danzolo211/Spotify_Frame/tools/_stand_preview.png

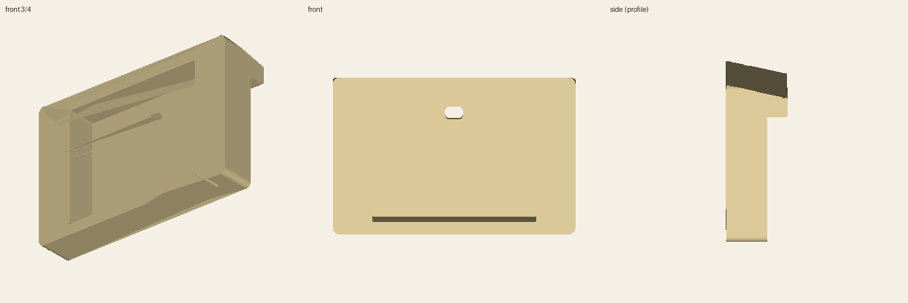
tools/_stand_preview.png
