danzolo211/Spotify_Frame/tools/_v3_cutaway.png

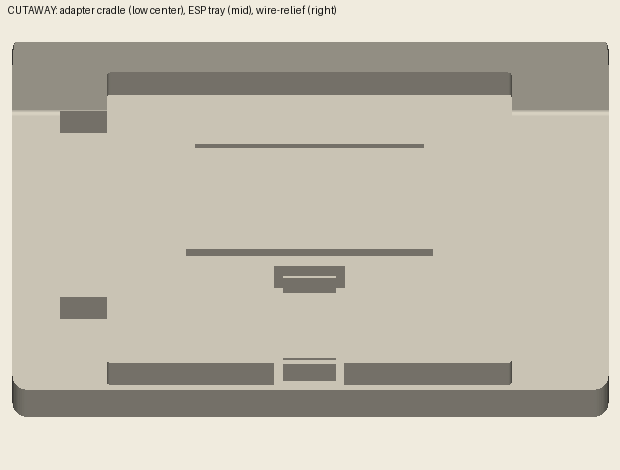
tools/_v3_cutaway.png
