danzolo211/Spotify_Frame/tools/_v3_fit_side.png

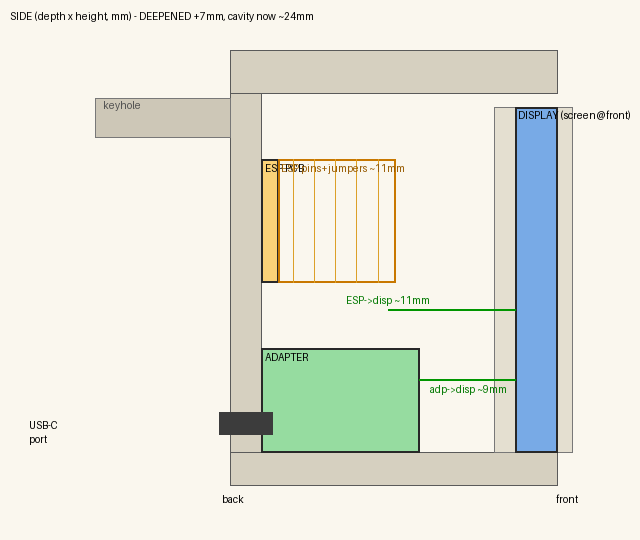
tools/_v3_fit_side.png
