danzolo211/Spotify_Frame/tools/_v3_preview.png

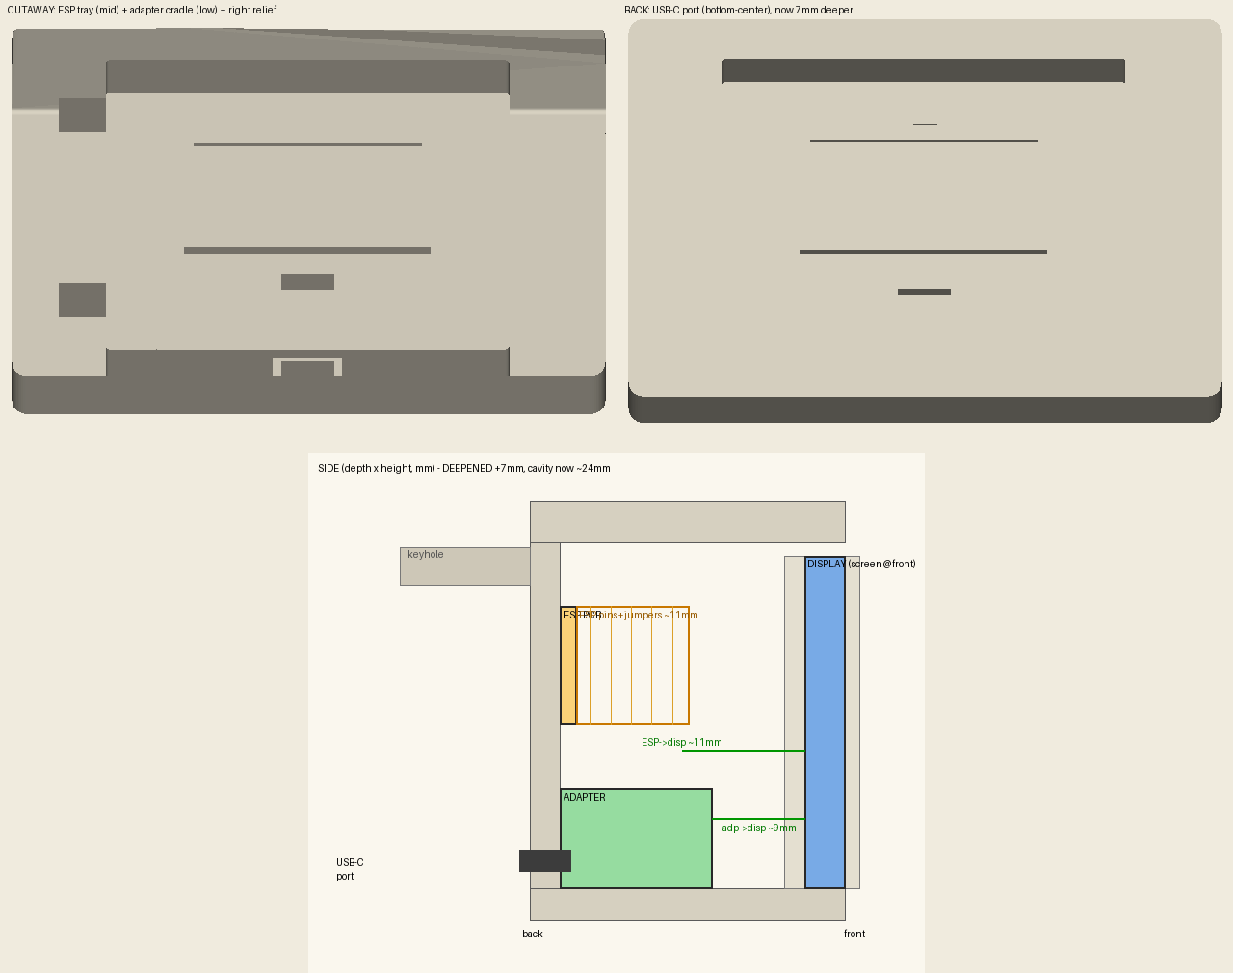
tools/_v3_preview.png
