danzolo211/Spotify_Frame/tools/previews/000_note-flourish.png

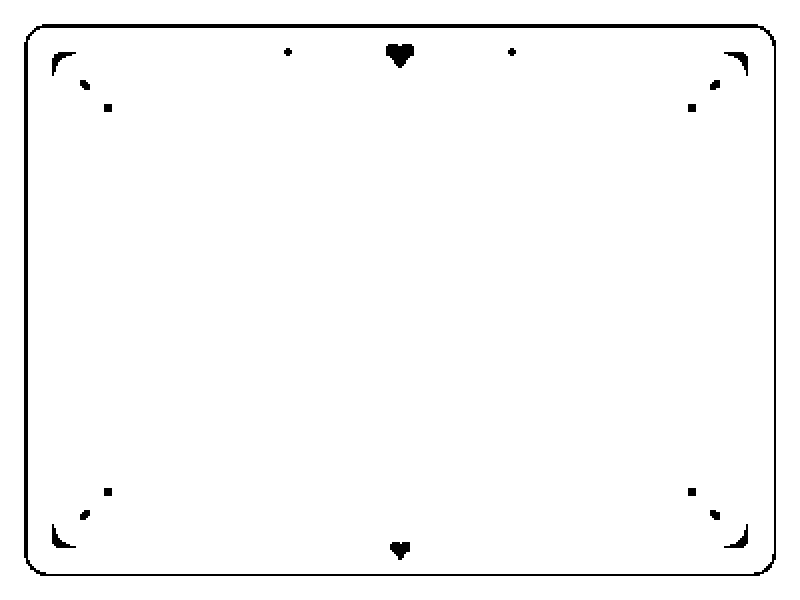
tools/previews/000_note-flourish.png
