danzolo211/Spotify_Frame/tools/previews/001_celebration.png

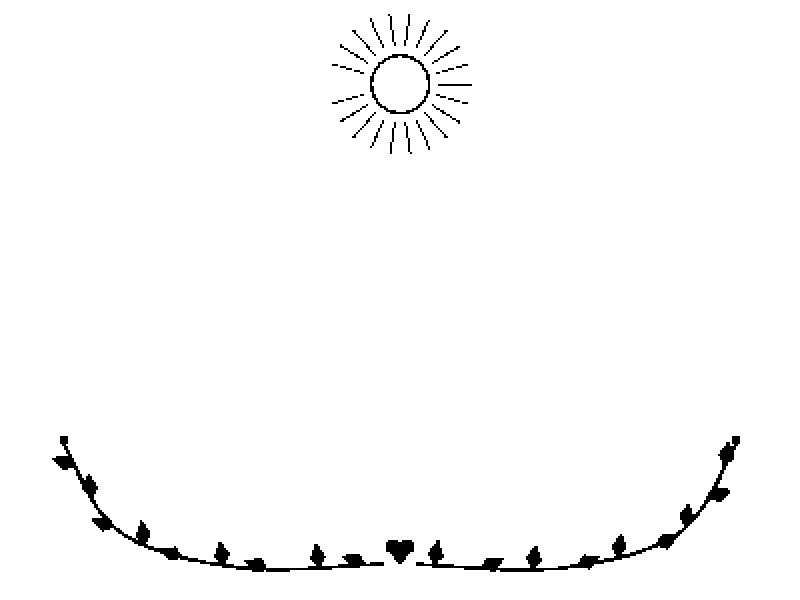
tools/previews/001_celebration.png
