danzolo211/Spotify_Frame/tools/previews/002_golgotha-dawn.png

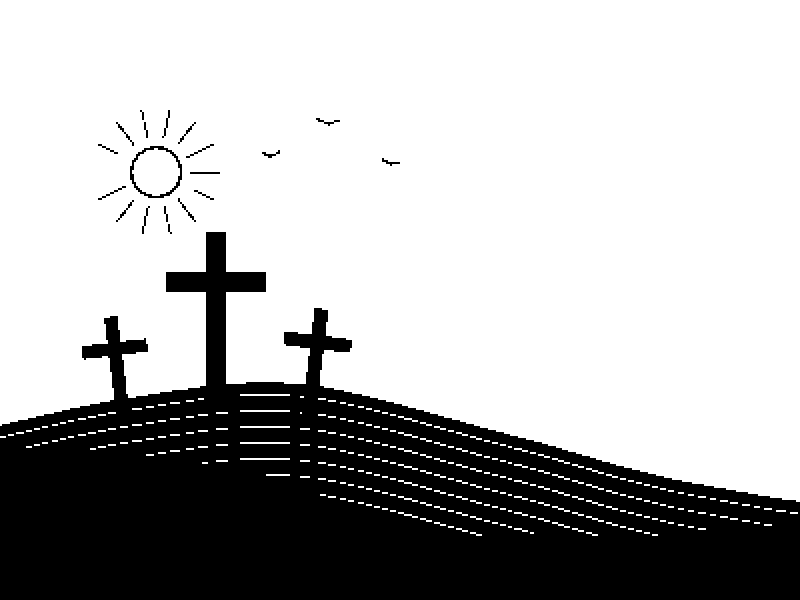
tools/previews/002_golgotha-dawn.png
