danzolo211/Spotify_Frame/tools/previews/003_shepherd.png

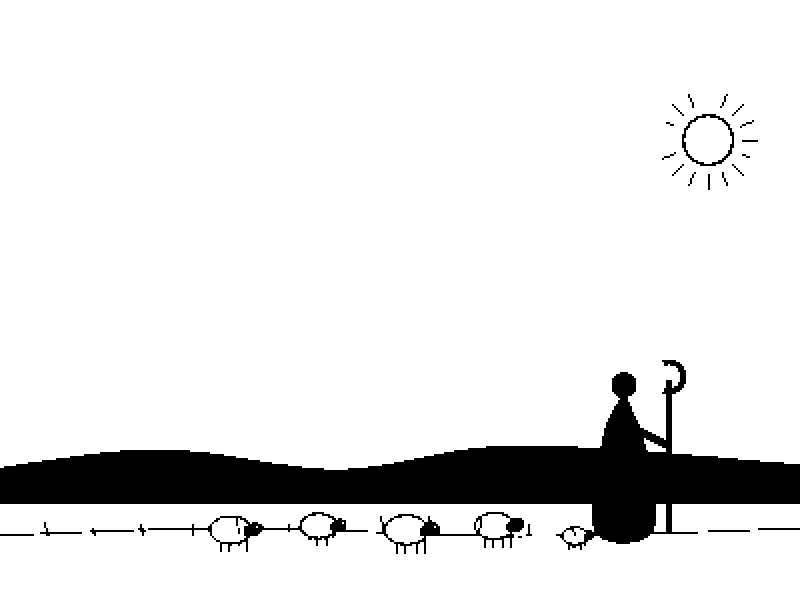
tools/previews/003_shepherd.png
