danzolo211/Spotify_Frame/tools/previews/004_lighthouse.png

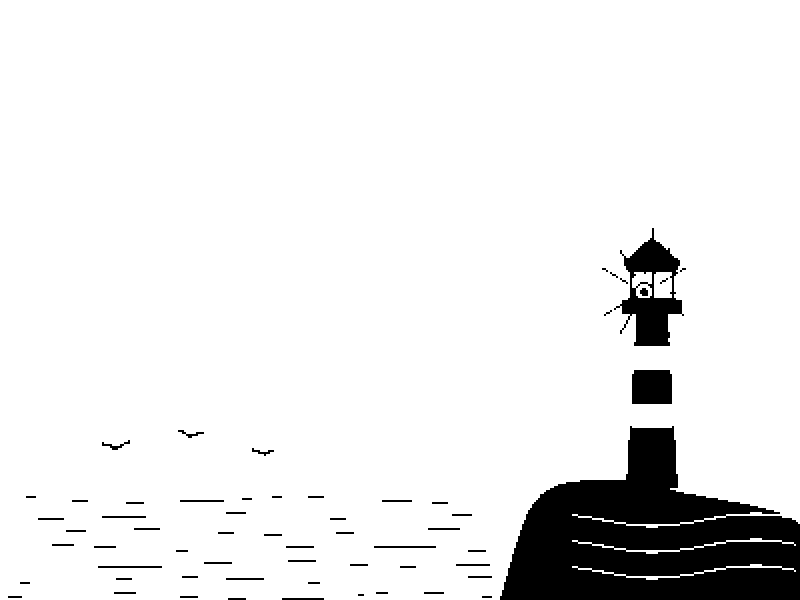
tools/previews/004_lighthouse.png
