danzolo211/Spotify_Frame/tools/previews/005_still-waters.png

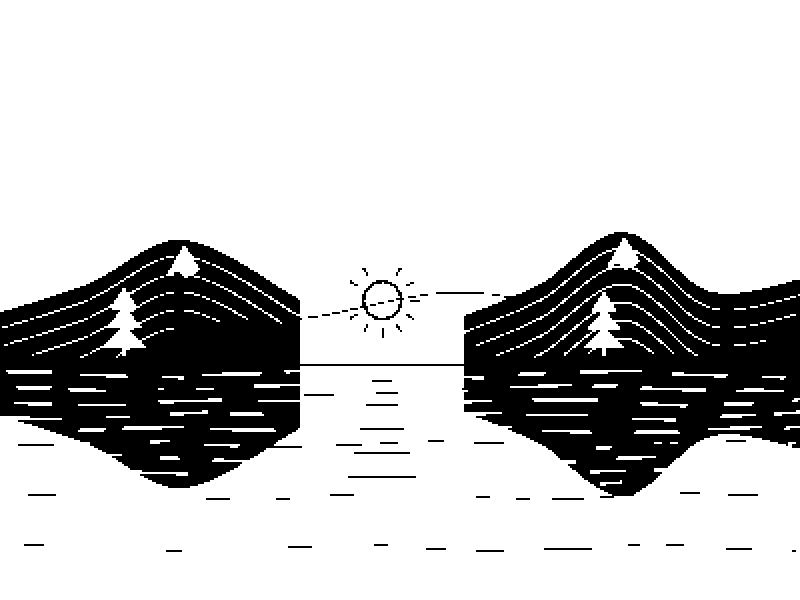
tools/previews/005_still-waters.png
