danzolo211/Spotify_Frame/tools/previews/006_empty-tomb.png

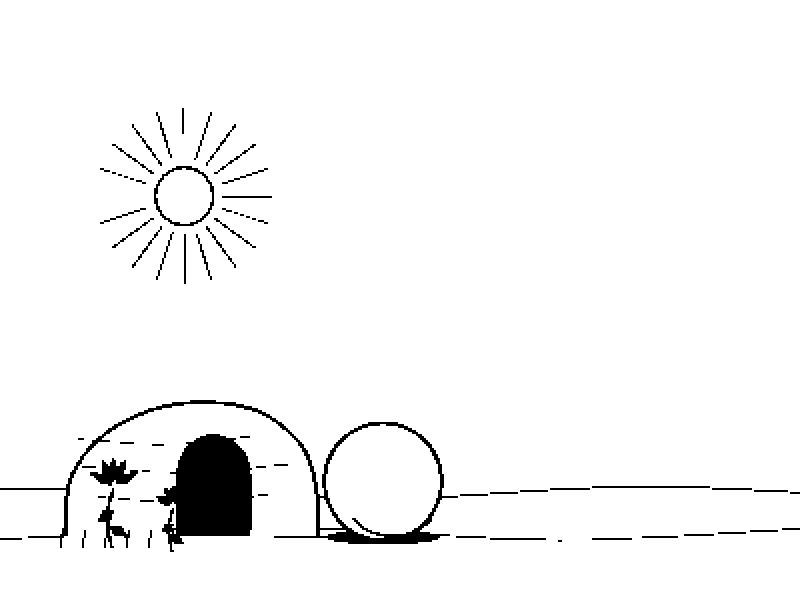
tools/previews/006_empty-tomb.png
