danzolo211/Spotify_Frame/tools/previews/007_botanical-frame.png

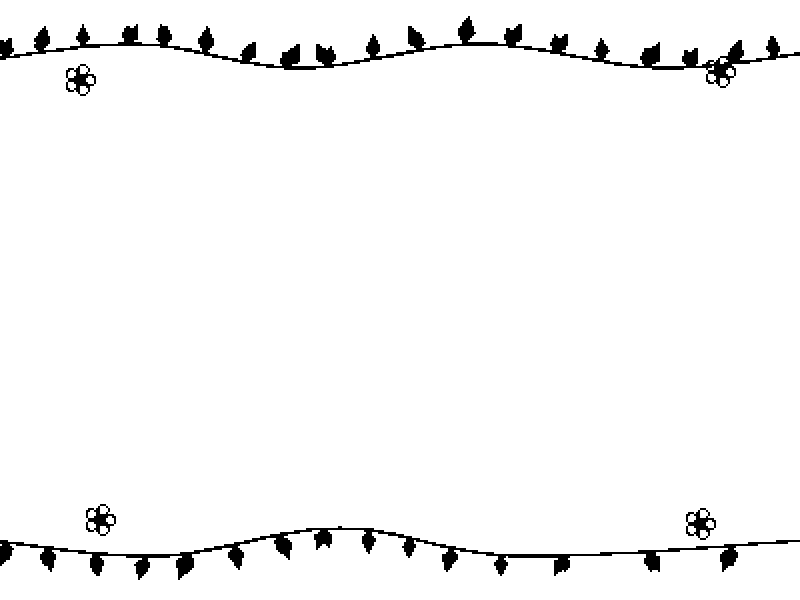
tools/previews/007_botanical-frame.png
