danzolo211/Spotify_Frame/tools/previews/008_dove-ascending.png

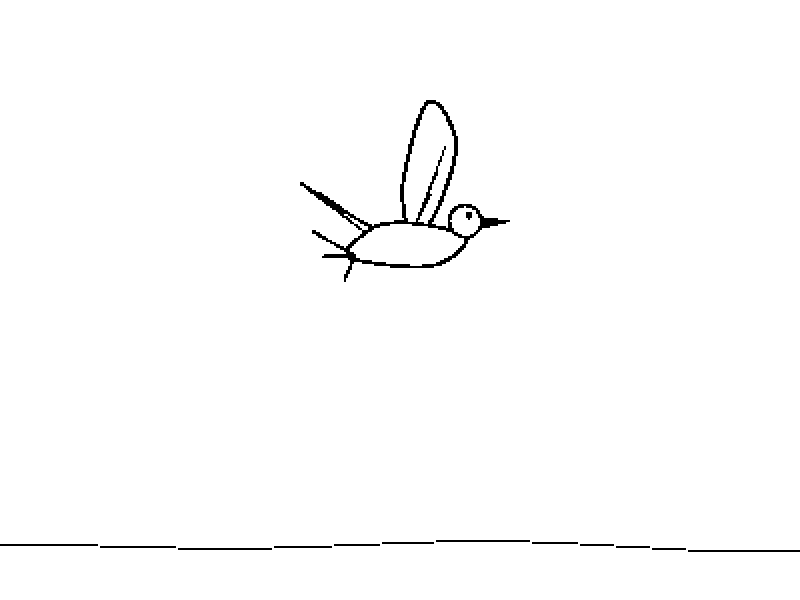
tools/previews/008_dove-ascending.png
