danzolo211/Spotify_Frame/tools/previews/009_mountain-path.png

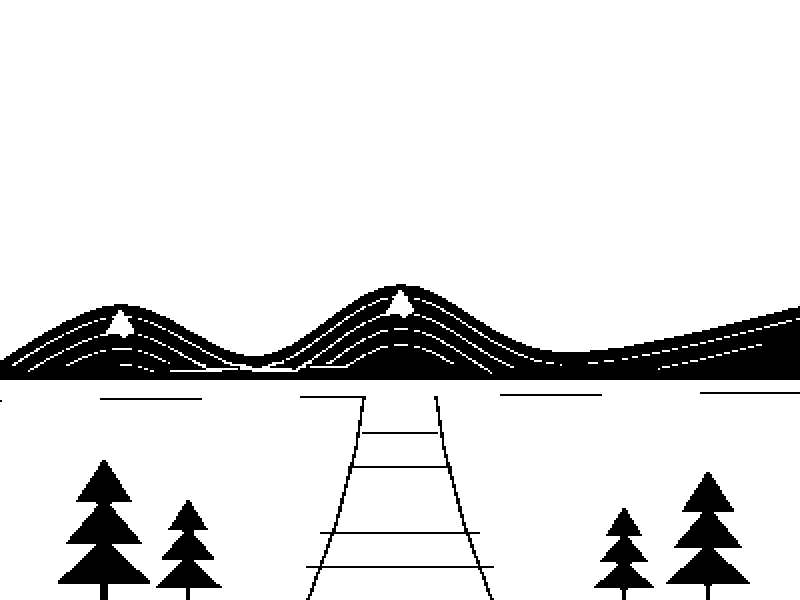
tools/previews/009_mountain-path.png
