danzolo211/Spotify_Frame/tools/previews/010_open-book.png

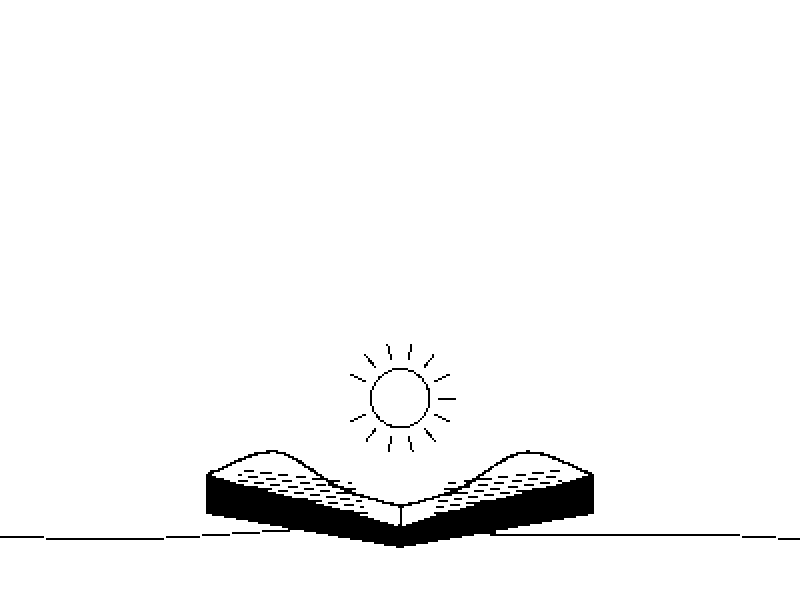
tools/previews/010_open-book.png
