danzolo211/Spotify_Frame/tools/previews/011_sailboat-dawn.png

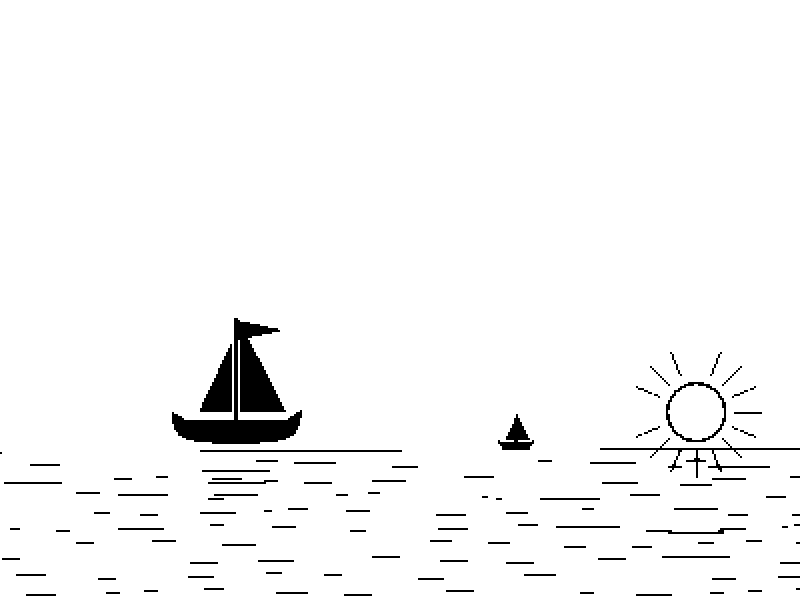
tools/previews/011_sailboat-dawn.png
