danzolo211/Spotify_Frame/tools/previews/012_starry-night.png

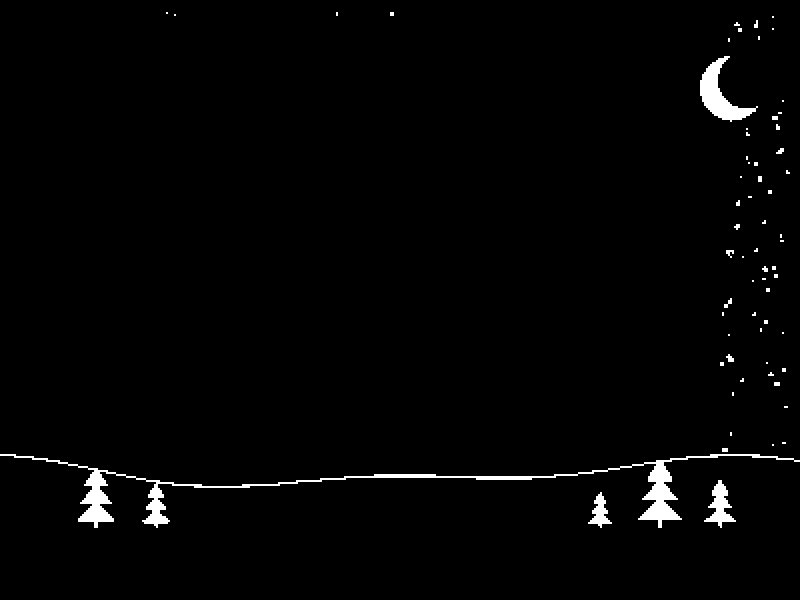
tools/previews/012_starry-night.png
