danzolo211/Spotify_Frame/tools/previews/013_moonlit-hills.png

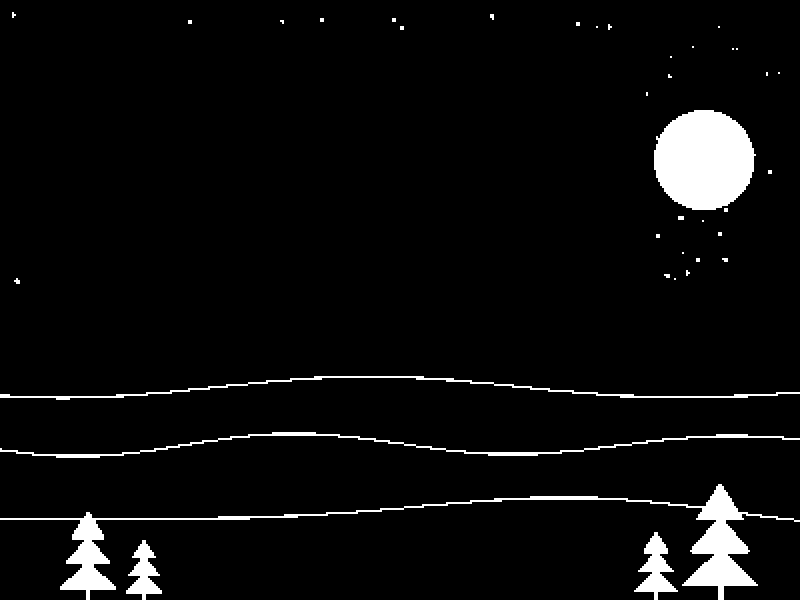
tools/previews/013_moonlit-hills.png
