danzolo211/Spotify_Frame/tools/previews/014_great-wave.png

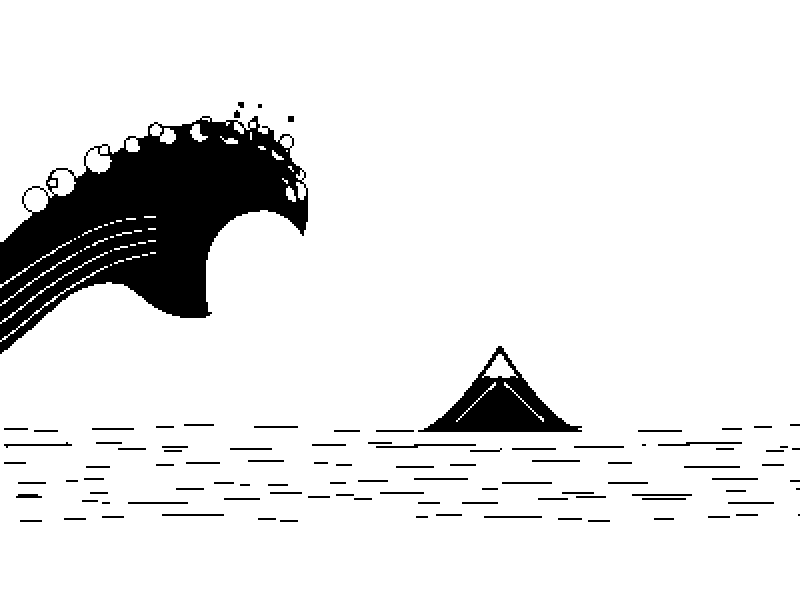
tools/previews/014_great-wave.png
