danzolo211/Spotify_Frame/tools/previews/016_crane-moon.png

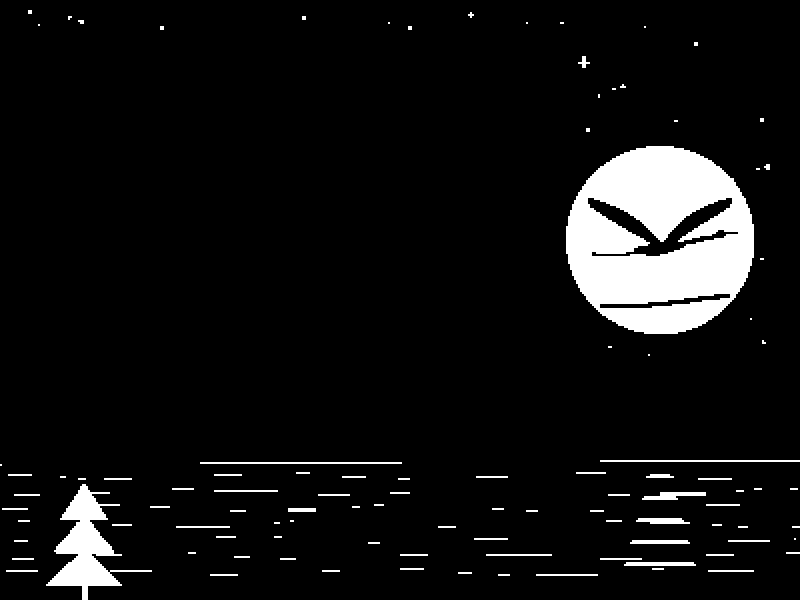
tools/previews/016_crane-moon.png
