danzolo211/Spotify_Frame/tools/previews/_ALL.png

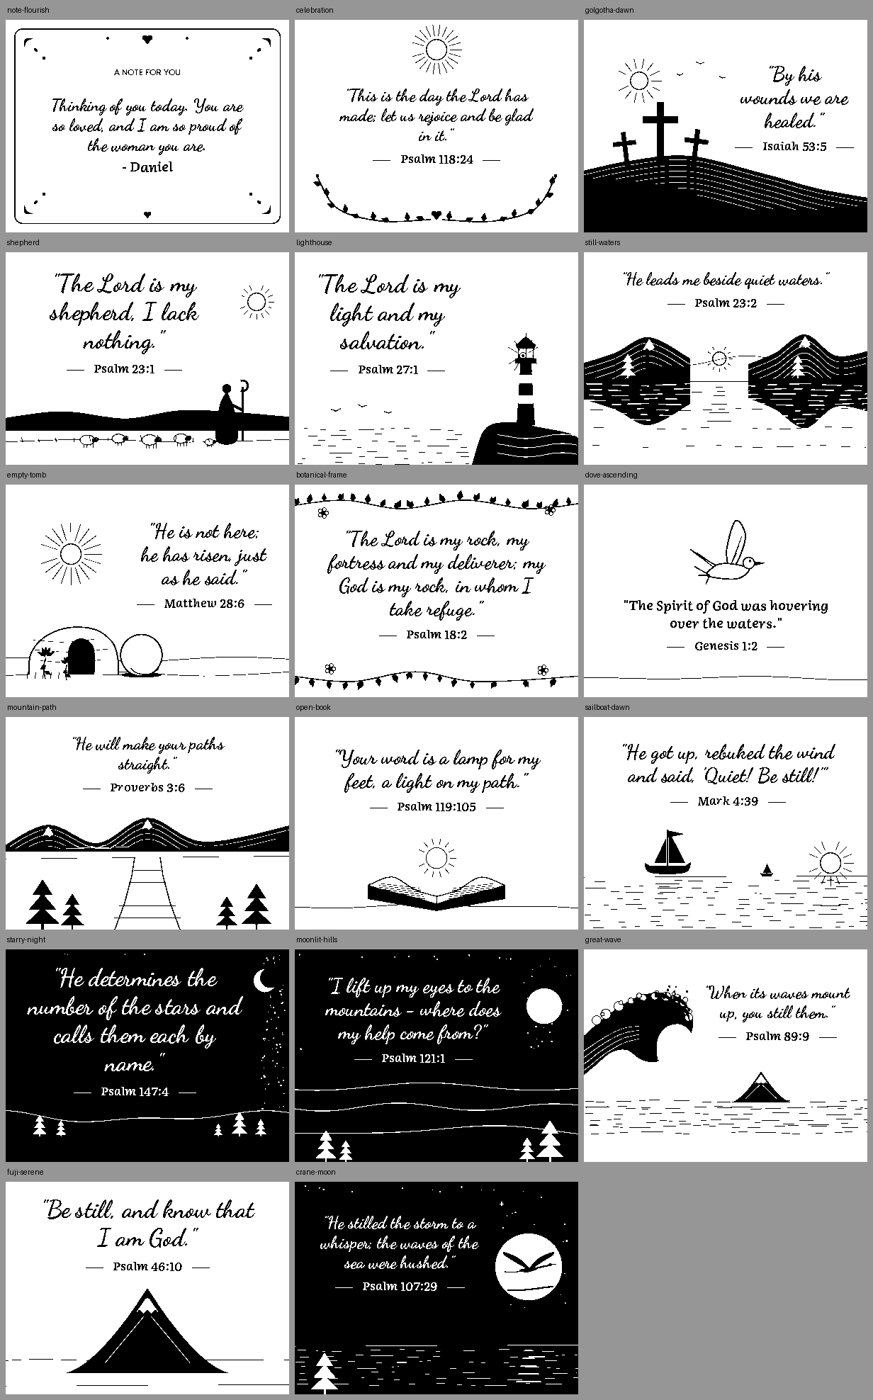
tools/previews/_ALL.png
