danzolo211/Spotify_Frame/tools/previews/_composed.png

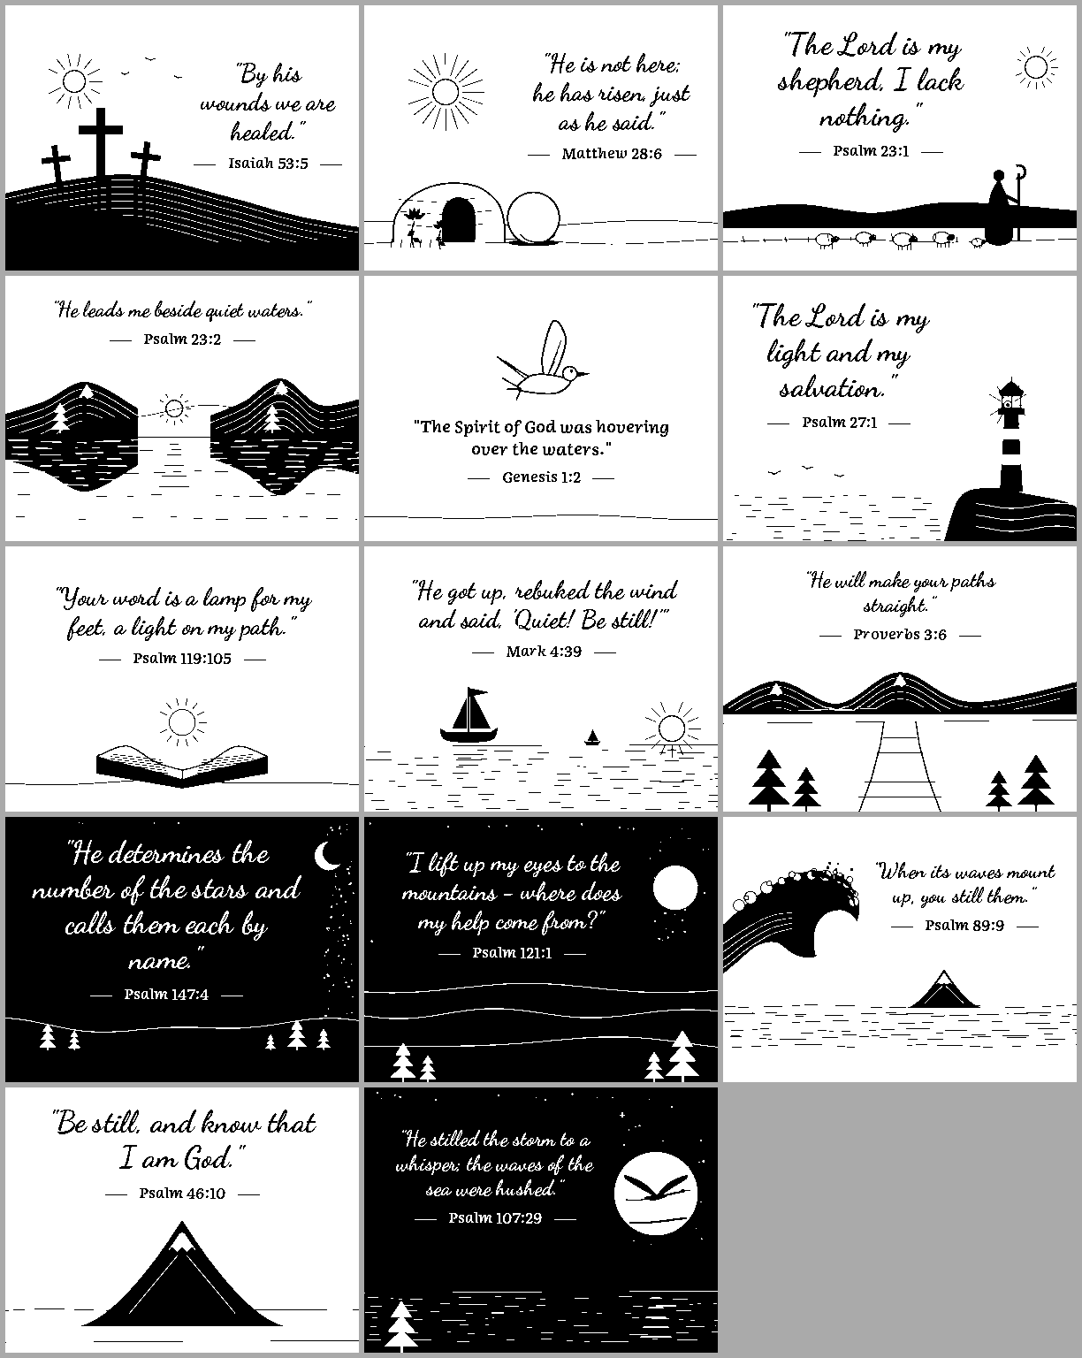
tools/previews/_composed.png
