danzolo211/Spotify_Frame/tools/previews/_sheet.png

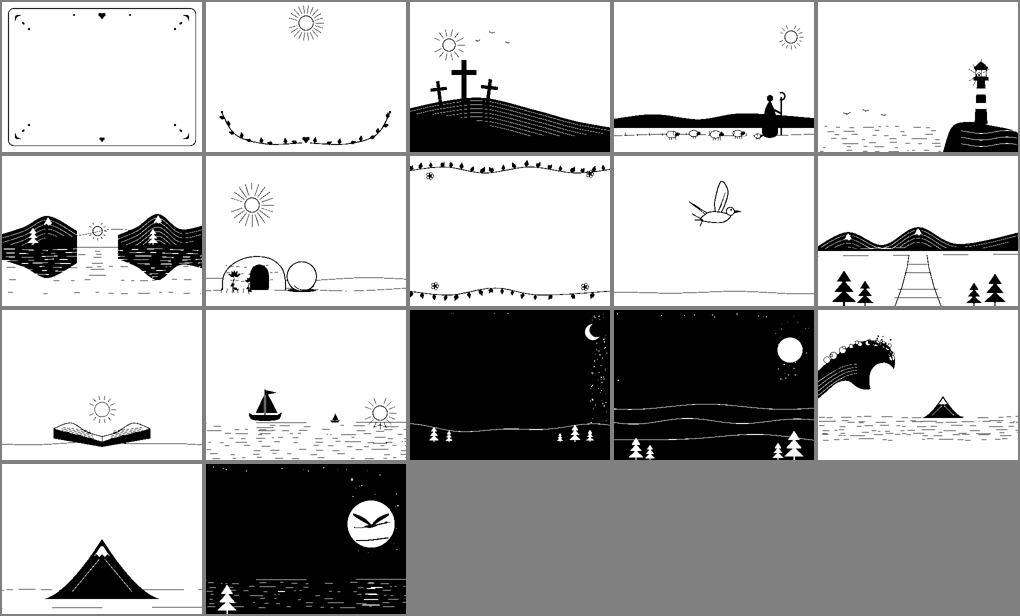
tools/previews/_sheet.png
