danzolo211/Spotify_Frame/tools/previews/app_scenes.png

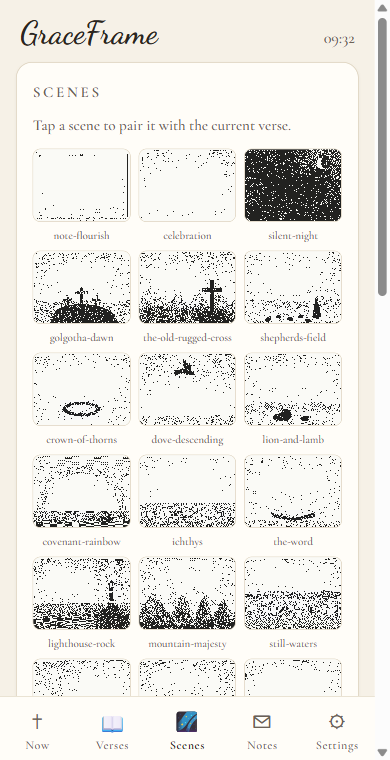
tools/previews/app_scenes.png
