danzolo211/Spotify_Frame/tools/previews/review/02_golgotha-dawn.png

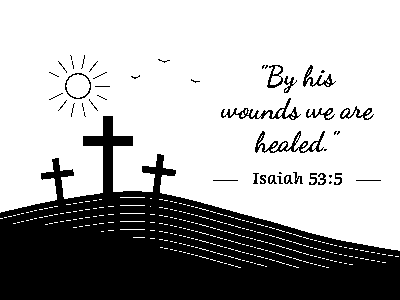
tools/previews/review/02_golgotha-dawn.png
