danzolo211/Spotify_Frame/tools/previews/review/03_shepherd.png

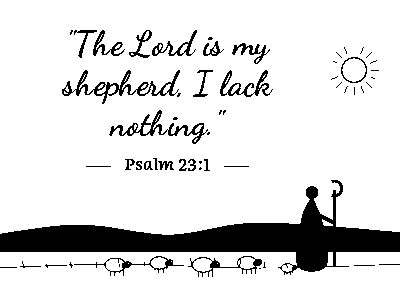
tools/previews/review/03_shepherd.png
