danzolo211/Spotify_Frame/tools/previews/review/04_lighthouse.png

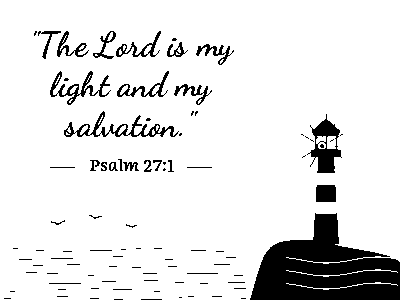
tools/previews/review/04_lighthouse.png
