danzolo211/Spotify_Frame/tools/previews/review/05_still-waters.png

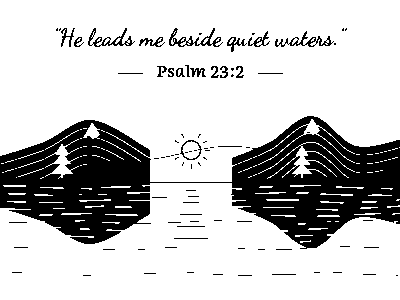
tools/previews/review/05_still-waters.png
