danzolo211/Spotify_Frame/tools/previews/review/06_empty-tomb.png

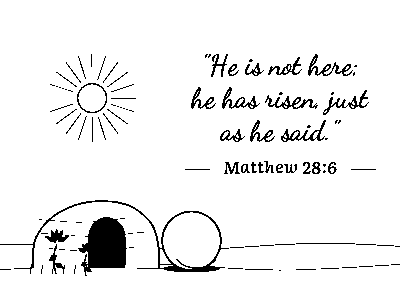
tools/previews/review/06_empty-tomb.png
