danzolo211/Spotify_Frame/tools/previews/review/07_botanical-frame.png

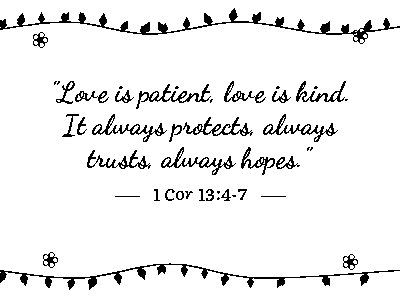
tools/previews/review/07_botanical-frame.png
