danzolo211/Spotify_Frame/tools/previews/review/08_dove-ascending.png

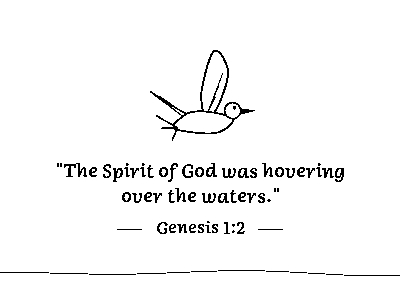
tools/previews/review/08_dove-ascending.png
