danzolo211/Spotify_Frame/tools/previews/review/09_mountain-path.png

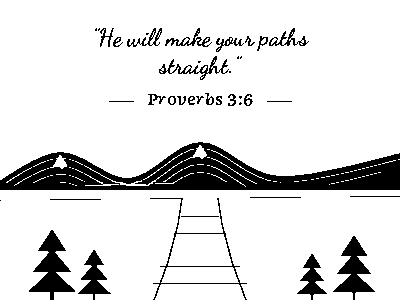
tools/previews/review/09_mountain-path.png
