danzolo211/Spotify_Frame/tools/previews/review/10_mountain-path_art.png

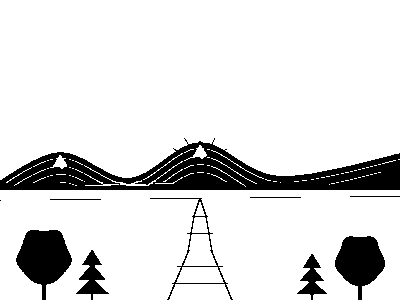
tools/previews/review/10_mountain-path_art.png
