danzolo211/Spotify_Frame/tools/previews/review/10_open-book.png

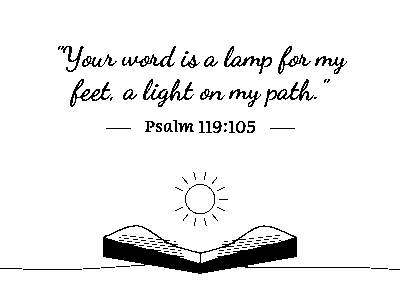
tools/previews/review/10_open-book.png
