danzolo211/Spotify_Frame/tools/previews/review/11_open-book.png

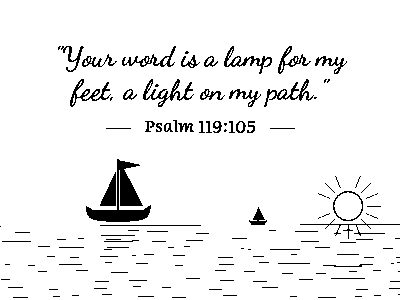
tools/previews/review/11_open-book.png
