danzolo211/Spotify_Frame/tools/previews/review/11_sailboat-dawn.png

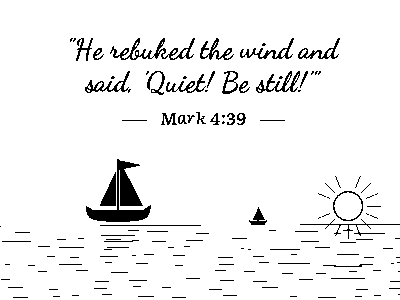
tools/previews/review/11_sailboat-dawn.png
