danzolo211/Spotify_Frame/tools/previews/review/12_starry-night.png

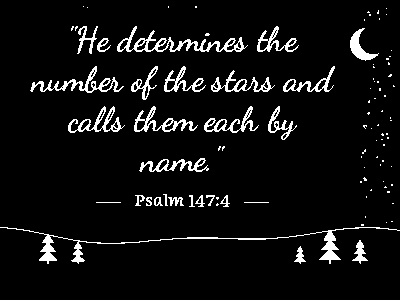
tools/previews/review/12_starry-night.png
