danzolo211/Spotify_Frame/tools/previews/review/13_starry-night.png

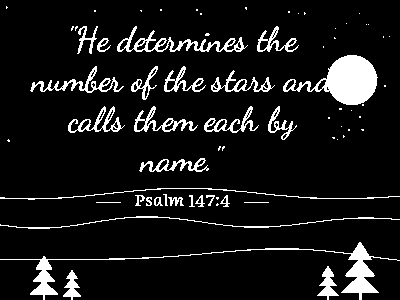
tools/previews/review/13_starry-night.png
