danzolo211/Spotify_Frame/tools/previews/review/14_great-wave.png

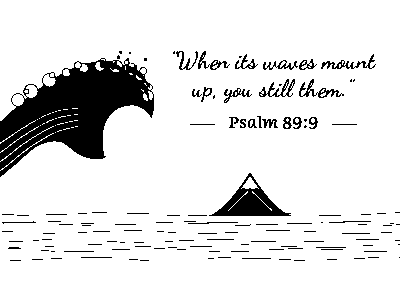
tools/previews/review/14_great-wave.png
