danzolo211/Spotify_Frame/tools/previews/review/14_moonlit-hills_art.png

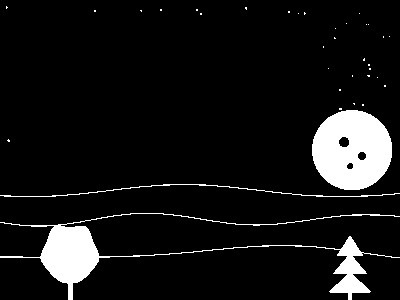
tools/previews/review/14_moonlit-hills_art.png
