danzolo211/Spotify_Frame/tools/previews/review/15_fuji-serene.png

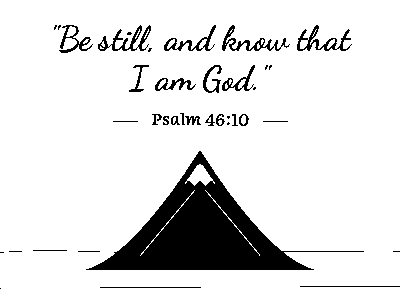
tools/previews/review/15_fuji-serene.png
