danzolo211/Spotify_Frame/tools/previews/review/15_great-wave.png

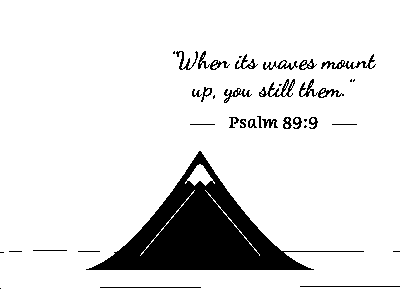
tools/previews/review/15_great-wave.png
