danzolo211/Spotify_Frame/tools/previews/review/16_crane-moon.png

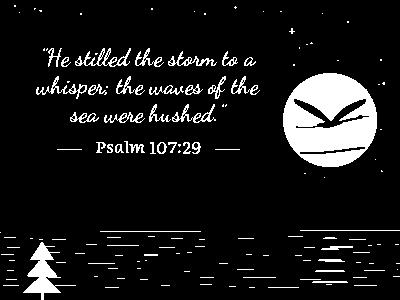
tools/previews/review/16_crane-moon.png
