danzolo211/Spotify_Frame/tools/previews/font_test.png

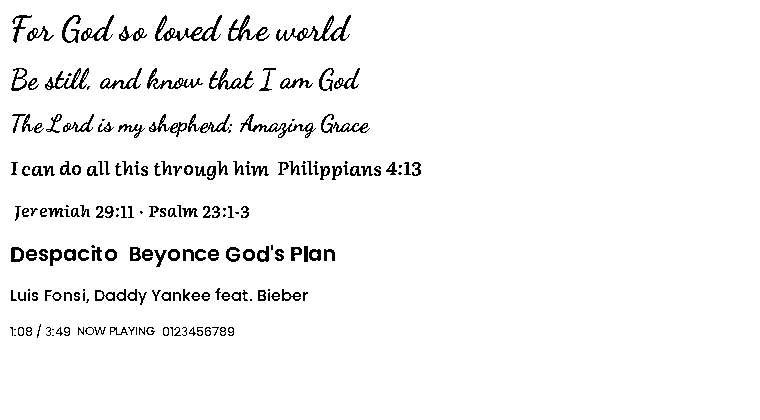
tools/previews/font_test.png
